VoltageFoundryMod/ForgeSeries/apps/gen/docs/Design.md

# GravityForge — Design

A dual physics-based generative sequencer for the Forge Series hardware.

Two virtual containers hold bouncing balls. Gravity pulls them down, the
containers rotate, and every time a ball strikes a peg on a container wall it
emits a note. The result is a rhythm that is repetitive enough to feel composed
but never quite loops — the Tombola idea, adapted to one encoder and a 128×64
screen.

The novel part of this module is the **proximity coupling**: the two containers
are drawn side by side and a single parameter slides them together. Apart, they
are two independent sequencers. Overlapping, collisions in one shove the balls
in the other. Fully merged, they share one space. It is one continuous knob from
"two sequencers" to "one entangled instrument", and you can see it happening.

---

## 1. Hardware contract

Shared Forge Series platform (XIAO RP2040, SSD1306 128×64, MCP4728 quad DAC,
rotary encoder + switch). See [ForgeSeries-Hardware].

### Inputs

| Jack | Range | Role |
| ---- | --- | --- |
| IN 1 | gate/trigger | Menu-selectable: CLOCK / RESET / KICK / SPAWN |
| IN 2 | **0–5 V** | Assignable modulation target |
| IN 3 | **0–5 V** | Assignable modulation target |

> **CV range.** The current hardware revision accepts **0–5 V only**. A later
> revision moves to ±5 V. Every modulation read therefore goes through a single
> helper, `CvNorm()` in `lib/cvInputs.hpp`, which returns a normalized `0..1`.
> When the bipolar hardware lands, that one function changes to return `-1..1`
> and the targets that want bipolar behaviour opt in via `CvBipolar()` — no
> target-by-target rewrite.

### Outputs

Mirrors NoteForge exactly, so the jack map is muscle memory across the series:

| DAC index | Jack | Signal |
| --- | ---- | --- |
| 0 | 1 | CV A — pitch of the last peg hit, container A |
| 1 | 2 | CV B — pitch of the last peg hit, container B |
| 2 | 3 | GATE A — envelope / trigger / gate |
| 3 | 4 | GATE B |

`OUT_CV(ch)` / `OUT_GATE(ch)` in `lib/pinouts.hpp` name these indices.

---

## 2. Why pegs live on the wall

Tombola draws notes as pegs _inside_ a rotating container. Simulating free-floating
pegs means testing every ball against every peg each step — O(balls × pegs),
which on a 133 MHz Cortex-M0+ with no FPU is the one thing that would blow the
CPU budget.

Putting the pegs **on the container wall** is both closer to the original (the
notes ring the container) and O(1): the wall collision is already being
computed, so the contact angle falls out for free, and the peg index is one
division.

```
contact angle (world)  φ = atan2(py - cy, px - cx)
container-local        φ' = φ - rotation
peg index              i  = floor(φ' / (2π / pegCount))  mod pegCount
```

No search, no per-peg distance test. This is the single decision that makes the
whole module fit in the time budget.

---

## 3. Float, not fixed-point

The first instinct on an FPU-less M0+ is Q16.16 fixed-point. Working the budget
out, that turns out to be unnecessary:

The steady-state (non-colliding) cost per ball per step is ~14 float ops —
integrate velocity and position (8), then the wall test `dx²+dy² > R²` (6). At
the design limit of 8 balls per container × 2 containers × 1 kHz that is
**224 k soft-float ops/sec**, roughly 11 M cycles/sec, or **~8 % of one core**.

The expensive calls — `sqrtf`, `atan2f` — happen only on an actual collision,
which is a handful of events per second per ball, not per step.

So the physics is written in plain `float`, matching the idiom of the rest of
the series (`lib/envelope.hpp`, `lib/quantizer.hpp`) and keeping it readable and
unit-testable. Fixed-point stays available as an optimization if a future
feature (ball–ball collision, many more balls) changes the arithmetic.

**Budget guard:** physics runs at a fixed 1 kHz on Core 0 with a hard cap of
`PHYS_MAX_STEPS_PER_CALL` catch-up steps, so a display stall or a slow I2C write
can never spiral into an unbounded catch-up loop.

---

## 4. Physics model

State per ball: position `(x, y)`, velocity `(vx, vy)`. Semi-implicit Euler at a
fixed 1 ms timestep — fixed-step is what makes the sim deterministic, and
determinism is what makes it unit-testable and identical in VCV Rack.

```
v += g · dt
p += v · dt
```

### Wall collision

A ball is in contact when `|p − c| > R − ballRadius`. On contact:

1. **Project back** onto the wall (prevents tunnelling / sticking).
2. **Reflect** the normal velocity component, scaled by restitution (BOUNCE).
3. **Add the wall's tangential velocity.** The wall is rotating at ω, so the
   contact point is moving at `ω × r`. Transferring a fraction of that
   (the SPIN coupling) is what makes a rotating container actually stir the
   balls rather than just spinning a decorative ring behind them. This is the
   mechanism that makes rotation musical.
4. **Emit** the peg hit for the contact angle, if that peg is enabled.

### Keeping the gate a gate

Three guards decide whether a contact becomes a note, and they are the
difference between a sequencer and a buzzer:

1. **`PEG_MIN_IMPACT_SPEED`** — a peg only speaks when it is actually struck.
   Grazes and settling contacts still resolve as collisions and still transmit
   through the coupling; they just make no note.
2. **Refractory windows** — each ball remembers the last peg it fired.
   Re-striking the same peg needs the full `PEG_REFRACTORY_US`; moving to a
   different one needs the shorter `PEG_MIN_INTERVAL_US`.
3. **`PHYS_MIN_BOUNCE_SPEED`** — a ball that has lost its energy is topped back
   up, so a patch never dies in a silent pile at the bottom. There are two
   different ways that can happen and they need different answers — see
   "Exhausted versus riding" below.

The interaction between (2) and (3) is the subtle part, and getting it wrong is
what turned the GATE jack into a continuous sawtooth in the first version. A
ball settling against a **rotating** wall registers a contact every step, and
because rotation keeps sliding a *new* peg underneath it, the short "different
peg" window applies every time rather than the long one. With the energy floor
set low (6 px/s) the ball vibrated against the rim instead of bouncing, and the
container fired ~33 times a second — the envelope was reset at ~90 % every time
and the output never returned to zero.

The floor therefore has to sit comfortably **above** the impact threshold. At
60 px/s a settled ball hangs for `2×60/220 ≈ 0.55 s`, so it ticks along at about
2 Hz instead of buzzing, and every one of those bounces is hard enough to
count as a strike. The result is ~6 hits/sec per container at the default.

That number then sets container A's envelope default: decay must be shorter than
the gap between notes (~160 ms) or the gate cannot finish, which is why A's
factory decay is 100 ms rather than something pad-like.
`Sequencer.GateReturnsToZeroBetweenHits` is the regression guard.

Container B ships at the opposite end and is sized the other way round — see
"The factory patch is two examples" below.

### GRAVITY as a rescaling of time

Both speed constants above are quoted at `PHYS_REF_GRAVITY` (220) and **scale
with `sqrt(g / PHYS_REF_GRAVITY)`**. While they were absolute, GRAVITY was very
nearly useless as a density control, and for a reason that is invisible from the
formula: the hang-time argument above (`2v/g`) only describes a *vertical* bounce
at the bottom of the bowl. Most contacts are ricochets across a container that is
only `2(R − ballR) = 36 px` wide, and a ball leaving the wall at the 60 px/s floor
crosses a mean chord of `4R/3 ≈ 24 px` in ~0.4 s **whatever gravity is doing**.
Turning gravity down gave flatter paths at the same note rate.

The simulation has exactly one length (`R`) and one acceleration (`g`), so its
natural speed is `sqrt(gR)` — which at the reference works out to 66 px/s, and is
why 60 was the right floor to begin with. Scaling both constants by
`sqrt(g/g₀)` makes GRAVITY a pure rescaling of time: under `v → v/k`,
`g → g/k²` the parabola `x = vt, y = gt²/2` traces the **identical path**, taken
`k` times slower. So the character of the motion, the distribution of contact
angles and the resulting peg pattern are all preserved exactly; only the tempo
moves. Measured, with three balls:

| GRAVITY | scale | hits/sec |
| --- | ----- | --- |
| 5 | 0.15  | 1.0 |
| 30 | 0.37  | 2.1 |
| 220 | 1.00  | 6.1 |
| 900 | 2.02  | 12.3 |

Three consequences worth stating, because each is a bug if forgotten:

- **The scale is floored** at `PHYS_MIN_SPEED_SCALE`. Gravity may legally be 0
  (a container stirred purely by its rotating wall), and an unclamped `sqrt`
  would take the energy floor to zero — balls coasting to a halt — *and* the
  impact threshold to zero, so every graze would speak. That is the buzzer
  failure mode reached from the opposite direction.
- **Reported hit energy is normalised** back into reference units before it
  leaves the physics. ACCENT maps a fixed 30..150 impact window onto gate level
  (`sequencer.hpp`); a slow container reporting its raw, small speeds would make
  every hit read as feather-light and collapse ACCENT to a constant.
- **The coupling uses the receiving container's threshold.** "Was that hard
  enough to ring?" is a question about the rim being struck, and A and B can be
  running very different gravities. Using the source's would let a heavy A
  machine-gun a becalmed B.

`Physics.TheReferenceGravityIsUnscaled` pins the compatibility claim: at 220 the
scale is exactly 1.0 and every number is what it always was.

The **three time constants** — `PEG_REFRACTORY_US`, `PEG_MIN_INTERVAL_US` and
`PHYS_REVIVE_US` — scale _inversely_ with the same factor. Speeds multiply by it,
times divide by it; that is what rescaling time means. Leaving the refractory
windows absolute caps every container at 83 Hz, which is invisible at the
reference where the natural rate is ~6 Hz, and wildly out of scale in a container
whose natural rate is 1 Hz — anything that does chatter down there then runs
completely unchecked.

### Exhausted versus riding

A ball stops making notes in two quite different ways, and conflating them was a
long-standing bug that the gravity scaling made much easier to hit.

**Exhausted** — the ball has genuinely run out of energy and is settling into a
pile at the bottom. Absolute speed is the right measure, an immediate top-up to
`PHYS_MIN_BOUNCE_SPEED` is the right response, and that is the original floor.

**Riding** — the ball has plenty of speed, but SPIN's grip has dragged it up to
the rim's own velocity. `vn`, the quantity that decides whether a strike speaks,
is measured _relative to the wall_, so a co-rotating ball registers nothing while
looking perfectly lively on screen. The absolute floor cannot see this at all: it
looks at a ball travelling at 226 px/s (SPIN 1 at 120 BPM) and correctly declines
to add energy to it.

This was already live before the gravity work: measured at that commit, **SPIN 1
produced 0.02 notes/sec at every gravity** — the container fired once and then
rode the rim in silence indefinitely. It went unnoticed because every physics
test in the suite ran with `omega = 0`. Scaling the speed constants with gravity
then spread the same failure up into the slower spins, since the floor fell below
the rim speed: SPIN 4 was silent at any gravity below ~80, which is exactly where
the ambient settings live.

The fix has two halves, and the second is as important as the first:

1. The floor is also evaluated in the **wall's frame**, which is the frame the
   note-making quantity lives in.
2. That revive is **rate-limited by whether the ball is actually failing to
   speak** — `lastHitUs`, the time of its last real strike. A bare wall-frame
   floor over-corrects badly: a dragged ball is below it on essentially every
   contact, gets re-launched every time, and with the rim sweeping past returns
   within ~10 ms. Measured, that turned the silence into a 45 Hz machine-gun.

So a ball riding the rim gets flicked off it a few times a second rather than
continuously. That is both musical and honest about the physics — a fast-spinning
bowl really does hold its contents against the wall.

One consequence worth stating plainly: **the rotating wall is an energy source
that does not scale with gravity.** At SPIN 1 or 1/2 the wall stirs the container
harder than gravity pulls on it, and GRAVITY loses most of its authority over the
density. SPIN 4 and slower leave it in charge. `Physics.NoSpinAndGravityCombinationGoesSilent`
sweeps all six spin rates × six gravities × both directions, which is the shape
of test this bug needed — any single pair looks fine, and the failure only shows
up as a hole in the grid.

### DENSITY and SPACE

Two controls sit at the very end of the hit path, after the physics has fully
resolved the bounce and after the peg mask:

- **DENSITY** — the percentage chance that a note which cleared everything else
  actually speaks.
- **SPACE** — a minimum gap between two notes from one container, set in beats
  and converted to µs against the live tempo by `ApplyParams()` (the container
  has no clock, exactly as with the loop period).

They exist because *every other* way of thinning the output — fewer balls, less
gravity, less bounce, fewer pegs — also changes how the container moves, and the
screen is half the instrument. A thinned note is a bounce you see and do not
hear, and `Physics.DensityDoesNotDisturbTheMotion` asserts the simulation stays
bit-identical.

SPACE is checked **first**, then DENSITY. SPACE is a hard ceiling on the rate and
DENSITY thins what got through, so the two compose rather than interact: at SPACE
1 beat and DENSITY 50 % you get "at most one note a beat, and about half the
beats speak". The reverse order would have DENSITY rolling dice on notes SPACE
was going to drop anyway.

Only a note that actually *speaks* restarts the SPACE window. Restarting it on a
dropped note would let a busy container gate itself into permanent silence after
its first note — `Physics.SpaceDoesNotStarveAfterDroppingNotes`.

Both live in `Container` rather than in the sequencer so they take part in the
loop snapshot: DENSITY draws from the container's PRNG and SPACE keeps a
timestamp, and if either sat above the snapshot boundary a "repeating" phrase
would quietly gain and lose notes on every pass. See §6.

### The factory patch is two examples

Because the containers are wholly independent at PROXIMITY 0, the boot patch can
be two worked examples rather than one, and it is:

| | A (OUT 1/3) | B (OUT 2/4) |
| --- | --- | --- |
| Rate | ~6.2 notes/s | ~0.45 notes/s |
| Physics | g 220, 3 balls, SPIN 8 | g 20, 1 ball, SPIN 16, bounce 0.45 |
| Notes | C major, SPREAD 2 | C pentatonic major, SPREAD 1, high |
| Gate | 0 / 100 ms | 120 / 750 ms |
| Thinning | none | DENSITY 85, SPACE 2 beats |

A is unchanged from the original factory patch, so patching only OUT 1 still
gives exactly what the module has always given. B exists to make the slow half of
the range audible without the user having to know it is there — which is the
thing a parking-lot feature usually fails at.

Three decisions in B are worth recording:

- **Its scale is a subset of A's.** The containers drift into every possible
  alignment, so B's notes have to be ones that cannot clash with A's whatever
  lands together. C pentatonic major (C D E G A) contains no semitone at all,
  which is what lets it sit under a busy C major sequence indefinitely.
- **SPIN stays slow.** The rotating wall is an energy source that does not scale
  with gravity, so a fast spin here would stir the container harder than gravity
  pulls on it and undo the slowness GRAVITY was set for.
- **The envelope is sized against SPACE's floor, not the average gap.** B averages
  ~2.3 s between notes but SPACE only guarantees 1 s, so attack + decay is
  120 + 750 = 870 ms. Sizing it against the average would look right on paper and
  clip on every close pair — the same mistake as A's decay, one order of
  magnitude further out.

`Physics.FactoryContainersSitAtOppositeEndsOfTheRange` pins the behaviour; the
Rack isolation test pins the settings themselves, including that the envelope
fits inside the SPACE floor.

---

## 5. Proximity coupling

Both containers have radius `R` and sit on the screen midline. A single
**PROXIMITY** parameter (0–100 %) sets the distance `D` between their centres:

```
D = D_MAX − proximity/100 × (D_MAX − D_MIN)

PROXIMITY 0%              PROXIMITY 55%           PROXIMITY 100%
   ___     ___              ___ _ ___                 _____
  / A \   / B \            / A X B \                 / AB  \
 |     | |     |          |    |    |               |       |
  \___/   \___/            \___|___/                 \_____/
    independent            overlap: coupled          merged: one space
```

Overlap fraction `k = clamp((2R − D) / 2R, 0, 1)` is the coupling strength.

When `k > 0` and a ball in A strikes the wall **at a contact point that lies
inside container B**, the collision transmits: an impulse is applied to B's
balls, directed away from the contact point, scaled by `k` and by the collision
energy, and falling off with distance. Symmetrically for B → A.

This is deliberately _energy_ transfer, not ball transfer. It means:

- the ball count in each container is stable and predictable
- each container keeps its own scale, peg layout and gravity

### What a transmitted strike plays

The energy arrives at a point on the receiving rim, so **the peg there rings** —
a real note and gate on that channel. The note is entirely the receiving
container's own (its peg ring, its scale, its SPREAD/BIAS, its muted pegs), so
nothing is copied across and a transfer can never sound out of key. Muting a peg
absorbs the transfer silently, which is how you shape which transfers speak.

Transmitted energy is scaled by COUPLE **before** the impact test, which is what
turns COUPLE into a musical gradient rather than an on/off switch — light
coupling only nudges trajectories, and the containers begin answering each other
audibly only as it comes up:

| PROXIMITY | COUPLE | A notes/s | B notes/s | transmitted/s | |
| --- | --- | --- | --- | --- | --- |
| 0 % | 60 % | 6.1 | 4.1 | 0.0 | apart — baseline |
| 60 % | 0 % | 6.4 | 4.6 | 0.0 | overlapping, coupling off |
| 60 % | 30 % | 6.0 | 4.2 | 3.8 | transmitting, too weak to ring |
| 60 % | 100 %  | 7.6 | 6.1 | 3.5 | starting to answer |
| 100 % | 100 %  | 10.3 | 9.9 | 10.5 | fully entangled |

Density roughly doubles at the extreme, which is the point of that setting. The
GATE jack still articulates there — measured 10.3 Hz, 0.00–5.00 V, idle 39 % of
the time with the 100 ms factory decay.

Transmitted strikes carry their own refractory, separate from the per-ball one,
because there is no ball behind them.

### Making it legible

The impulse is strong — measured against an identical uncoupled world it
displaces balls by **~13 px on a 40 px container**:

| PROXIMITY | separation | overlap | transmitted strikes/s | displacement |
| --- | --- | --- | --- | --- |
| 0 % | 48 | 0.00 | 0.0 | 0.00 px |
| 40 % | 28.8 | 0.28 | 3.0 | 13.5 px |
| 100 % | 0 | 1.00 | 12.4 | 13.6 px |

But strength was never the problem. Coupling fires a handful of times a second
while both containers are *already* bouncing several times a second, so with
nothing tying cause to effect the control reads as if it does nothing at all —
you cannot see a counterfactual.

So a transmitted strike raises a **spark**: an expanding double ring drawn at the
contact point for a few frames. That one cue is what turns PROXIMITY from
"apparently inert" into something you can watch working.
`Physics.CouplingRaisesAVisibleSpark` guards it.

Note the tests here deliberately assert *magnitude*, not mere non-zero
divergence. An earlier version only checked the two worlds differed by 0.01 px,
which any chaotic perturbation satisfies — it would have passed even if coupling
were imperceptible.

### Portals — deferred

Ball _transfer_ between containers is a natural extension of exactly this
geometry: the arc of A's wall that lies inside B is already computed, so opening
it and moving the ball into B is a small change. It is deliberately **not** in
v1 — it makes ball counts drift, and it is easy to end up with every ball in one
container and silence in the other. `PhysicsWorld::OverlapArc()` is written and
tested so this stays cheap to add later.

---

## 6. Timing

Physics **always free-runs.** Collisions produce note events the instant they
happen — that organic, never-quite-on-grid feel is the whole point.

Optionally, those events can be deferred to a clock grid:

```
QUANTIZE:  OFF | 1/4 | 1/8 | 1/16 | 1/8T | 1/16T
```

With quantize on, a peg hit is queued and released on the next division
boundary. **Drop rule:** if a second hit arrives for the same channel before the
pending one is released, the newer hit replaces it (last-wins). Stacking would
produce a burst of retriggers at the boundary; last-wins keeps the density
sounding like the physics that produced it.

The clock itself is the internal BPM (20–300, default 120), or an external clock
at IN 1 when that jack's role is CLOCK (interval between edges → BPM, median of
the last few intervals so one jittery edge does not lurch the tempo).

### Configured vs actually running

`Clock` tracks two separate things, and conflating them is a bug:

- `IsExternal()` — IN 1 is *configured* as a clock input. A menu setting.
- `IsExternalLive()` — and pulses are *actually arriving* right now.

The hardware has no switched jacks, so it cannot tell a patched cable from an
unpatched one — but it can tell whether edges are coming in, and that is the
thing that matters. CLOCK is IN 1's default role, so keying anything off
`IsExternal()` means the module declares itself externally clocked from the
moment it powers on, and the "e" badge on the home screen never tells you
anything.

Liveness needs a measured *interval*, not just one edge, and it lapses if no
pulse arrives within three intervals (clamped to 0.5–5 s). Scaling the timeout
to the observed tempo matters: a 30 BPM clock at 1 ppqn is 2 s between pulses,
so a short fixed timeout would declare it dead between every beat, while a long
fixed one would leave a fast clock hanging for seconds after it stops.

When liveness lapses the tempo falls back to the internal BPM and the interval
history is cleared. Without that, unplugging a clock leaves the containers
turning at whatever tempo was last derived, with the internal setting ignored
for ever.

Rotation is tied to the clock rather than set in raw degrees/sec, so the
containers stay musically related to the patch: **SPIN** selects beats per
revolution (`1/2/4/8/16`, plus reverse), and there is a FREE setting for when you
want it detached.

### Loop mode — keeping a phrase

The module's one real weakness is that a passage you like is gone before you can
reach the encoder. The fix falls out of determinism: the same state, stepped the
same number of times, produces the same notes. So a phrase is nothing more than a
snapshot plus a step count. Capture the balls, the rotation and the `PhysRandom`
state; run N beats' worth of steps; put it all back.

Three decisions make it hold together, and each of them is the difference
between a phrase that repeats and one that only nearly repeats:

**The rewind lands on an exact step, not on elapsed time.** `LoopTick()` runs
inside `PhysicsWorld::Advance()`'s stepping loop and counts steps. Scheduling it
from wall time would put the boundary a step early or late depending on how the
caller was interrupted, and one step of divergence in a chaotic system is a
different phrase within a few repeats.

**The simulation runs on its own clock.** `_simUs` advances exactly
`PHYS_STEP_US` per step and is what the peg refractory windows are measured
against. Previously the wall time was passed down, which meant identical ball
states could clear a 12 ms window on one pass and miss it on the next depending
on how many catch-up steps a call happened to batch. Free-running that is
invisible; looping it is fatal.

**Hit timestamps travel as ages, not absolute times.** The refractory guards ask
"how long since this ball last spoke". A restored absolute timestamp would sit
further into the past on every repeat, so the first bounce of each loop would
eventually clear a window it had not cleared the first time and the phrase would
gain a note it never contained.

What is deliberately _not_ snapshotted is the parameter set — gravity, spin, the
peg mask, proximity, the scale. Restoring those would make the loop fight the
menu and freeze CV modulation, when the reason to lock the motion is so you can
keep playing everything else over the top of it.

**NAP/WAKE** then mutes whole loops per container, with **SHIFT** offsetting each
container's place in that cycle — wake 1 / nap 1 with B shifted by one is
call-and-response for the cost of one menu row. The physics keeps running through
a nap and only the voice is silenced (`GravityChannel::SetMuted`), so a container
returns exactly where it would have been rather than restarting.

A change to **BEATS** re-arms and captures a new phrase; a change of _tempo_ does
not, or an external clock wandering by a BPM would re-arm every pass and the loop
would never repeat at all. `Reset()` re-arms too, which is what gives Randomize a
freshly captured phrase without any code of its own.

---

## 7. Pitch

Reuses NoteForge's `Quantizer` and `scales.hpp` unchanged — the peg ring is
just an index into the quantizer's table of enabled semitones.

Everything is counted in **scale degrees**, never semitones, so no combination of
settings can produce an out-of-key note, and the interval between adjacent pegs
follows the scale — a third in major, something else in pentatonic. Same
reasoning as NoteForge's degree-based transposition.

### SPREAD and BIAS

There is deliberately **no separate octave row.** An octave offset on its own only
slides the ring up and down; it says nothing about how wide the ring is or how the
notes sit inside it. So the register lives on the ROOT row it belongs to (see
"Where the span sits" below) and the two rows it would have cost do the work an
offset cannot:

- **SPREAD** — how many octaves the ring covers (1–5), counted up from ROOT and
  independent of peg count.
- **BIAS** — where inside that span the notes crowd (−100 low … 0 even … +100 high).

```
peg i   t     = i / (pegCount - 1)              fraction around the ring
        gamma = 2^(-|bias| / 70)                always <= 1
        warp  = bias >= 0 ?  t^gamma            crowd high
                          :  1 - (1-t)^gamma    crowd low  (mirror image)
        degree   = base + round(warp * span)
        semitone = quantizer.SemitoneAt(degree)
```

Warping `t` moves the notes in between **without moving the ends** (measured,
and asserted by `Sequencer.BiasTableMatchesTheDocumentedNotes`):

```
8 pegs, C major, ROOT C4, SPREAD 2   (0–2 V)

BIAS   0  (even)    C4  E4  G4  B4  D5  F5  A5  C6
BIAS -100 (low)     C4  D4  E4  F4  G4  A4  C5  C6
BIAS +100 (high)    C4  C5  E5  F5  G5  A5  B5  C6
```

Fixed endpoints are what make the two controls independent: the ring always
covers exactly the octaves SPREAD asks for, and BIAS only decides the
distribution inside it.

The two directions are **mirror images** rather than `gamma` vs `1/gamma`,
because the warp is discretised onto whole scale degrees. A steep curve near
`t = 0` rounds several pegs onto the same bottom note while the same curve near
`t = 1` spreads them out, so a plain `t^gamma` crowded low far harder than it
crowded high — at full negative bias it stacked three of eight pegs onto the
root while full positive bias produced no duplicates at all. Mirroring makes the
control behave identically in both directions, and neither extreme stacks pegs.

### Where the span sits — ROOT is an absolute note

**The ring starts on ROOT and opens upward by SPREAD.** ROOT therefore carries an
octave — it is `C4`, not `C` — and it is the module's register control.

It did not always work that way, and the first version is instructive. With ROOT
as a bare pitch class nothing anchored the register, so the span was **centred in
the output range and snapped to whole octaves**: a reasonable-sounding rule that
turns out to be unusable, because the one thing the user cannot then do is
choose where the notes are. Two pegs over one octave landed two octaves up, and
no control on the module would move them. "Centred" is a decision the module has
no business making — it is the first thing a player wants to state.

Folding the octave into ROOT rather than adding a row is forced by the six-row
page limit, and it turns out to be the better UI anyway: "the ring starts on this
note" is one idea, and the row that names the note is where you look for it. The
menu edits it as a single semitone number so one detent is a semitone, and the
displayed octave has 0V NOTE applied, so the row reads as the note the
oscillator will play.

The octave is capped at `QUANT_OCTAVES - SPREAD` so the whole ring fits under
5 V, and widening SPREAD walks ROOT down rather than letting the top of the ring
flatten against the ceiling. A root part-way up the top octave can still leave
the ring a degree or two short of its full span; `SemitoneForPeg` covers less
rather than stacking the last pegs onto one note, which reads as a fault.

The lowest peg is the root itself — `IndexAtOrAbove`, never the _nearest_ degree,
so a hand-edited note mask that switches the root off moves the ring up to the
next available note instead of below the note the row names.

### What the notes are called — 0V NOTE

The jacks are the MCP4728's **0–5 V and nothing else**: five octaves at 1 V/oct,
with no negative rail to reach below 0 V. So the one thing the module can get
wrong about pitch is not the voltage but the _name_ — which note the patch
considers 0 V to be. That is a fact about the oscillator on the other end of the
cable, not about this module, so it is a setting: **SETTINGS ▸ 0V NOTE**, C0–C5,
default **C4** (VCV Rack's convention, and the common one on hardware VCOs).

Everything follows from it:

```text
volts(note) == octave(note) - 0V NOTE

0V NOTE = C4    range C4 (0 V) .. C9 (5 V),   SPREAD 2 ring = C6..C8
0V NOTE = C2    range C2 (0 V) .. C7 (5 V),   SPREAD 2 ring = C4..C6
```

It renames, it never transposes — the voltage on the jack is identical at every
setting, and SPREAD keeps sole control of where inside the range the notes sit.
Naming it after the thing it sets ("the note at 0 V") rather than REF or TUNING
is deliberate: both of those read as if turning them moves the pitch, which on
unipolar hardware is the one thing it cannot do.

It was previously fixed at C0, which is why a note the screen called C2 came out
of a Rack VCO — where 0 V is C4 — as C6. The setting is stored in the preset, so
a patch keeps the tuning of the rack it was built in.

Because a peg's pitch now depends on the peg *count* (it sets where each peg
falls within the span), the count travels with the hit — including a deferred
one, whose count must be the one that was in force when the ball actually
struck.

Per container: scale, root (with its octave), spread, bias, peg count (4–16), and
a peg enable mask so individual pegs can be silenced to open up the rhythm.

---

## 8. Screen

`R = 20 px`, centres on `y = 32`, so the containers occupy rows 12–52 and leave
a header row and a footer row.

```
 0        BPM 120   SPIN 4   CPL 55%          <- header
 12   .-""-.   .-""-.
      /  o   \ /   *  \                        <- containers slide together
 32  |    o   X   *    |                          with PROXIMITY
      \   .  / \  o   /
 52    '-..-'   '-..-'
 54       C3            G4                     <- live note per channel
```

Pegs are drawn on the wall: a solid 5 px dot when enabled, a small hollow ring
when muted, and a 7 px blob for a few frames after firing. Sizes are set by the
tightest case — at 16 pegs the rim gives 7.9 px of spacing, so a 5 px dot still
leaves clear air between neighbours while the 7 px flash fills the gap and makes
a hit unmistakable.

Balls are drawn at their true simulated radius (`PHYS_BALL_R`, 5 px across) —
filled for container A, hollow-with-a-centre-dot for B, so the two populations
stay distinguishable once PROXIMITY merges them into one space. Drawing the real
radius is the point of working in screen pixels: the ball you see is the ball
being simulated, so it never appears to sink into or float off the wall.

Rendering runs on **Core 1** exactly as in NoteForge, so the 20 Hz redraw never
stalls the 1 kHz physics on Core 0.

---

## 9. Menu map

| Group | Page | Contents |
| ----- | --- | --- |
| 0 | HOME | the physics view (custom renderer) |
| 1 | CLOCK | BPM, spin, quantize, IN1 role |
| 2 | COUPLING  | proximity, coupling amount, reset/kick actions |
| 3 | A PHYSICS | gravity, bounce, balls, spin ratio |
| 4 | B PHYSICS | same, container B |
| 5 | LOOP | phrase length, nap/wake, shift, new phrase |
| 6 | A NOTES | scale, root+octave, spread, bias, pegs, density |
| 7 | B NOTES | same, container B |
| 8 | A GATE | mode, attack, decay, level |
| 9 | B GATE | same, container B |
| 10 | CV | IN2 target, IN3 target, depths |
| 11 | SETTINGS  | 0V NOTE, screen timeout, boot menu |

LOOP sits after the two PHYSICS pages rather than next to CLOCK: its shift and
nap/wake settings are read per container, so it belongs with the rest of the
per-container editing rather than in the clock-domain block at the top.

Every page except HOME is a plain list handled by the existing generic
`MD_RenderGroup()` — no new rendering code per page.

---

## 10. File map

New to this module:

| File | Purpose |
| --- | --- |
| `lib/physics.hpp` | `Ball`, `Container`, `PhysicsWorld` — the simulation and coupling |
| `lib/sequencer.hpp`  | `GravityChannel` — container + peg→note mapping + envelope |
| `lib/clock.hpp` | internal/external clock, spin rate, quantize grid |
| `lib/cvInputs.hpp` | 0–5 V acquisition, `CvNorm()`, target matrix, IN 1 role |
| `lib/menuRender.hpp` | the physics home screen |

Carried over from NoteForge essentially unchanged: `quantizer.hpp`, `scales.hpp`,
`envelope.hpp`, `displayManager.hpp`, `menuDisplay.hpp`, `menuDefinitions.hpp`,
`boardIO.hpp`, `storage.hpp`, `calibration.hpp`, `calibrationData.hpp`,
`encoder.hpp`, `utils.hpp`, `splash.hpp`.

---

## 11. Constraints inherited from the platform

- Anything in `lib/` must compile for **both** the RP2040 and the VCV Rack shim.
- Core 1 owns `Wire` (display); Core 0 owns `Wire1` (DAC). Never cross them.
- `micros()` is the only clock — every time-dependent subsystem takes the
  timestamp as a parameter, which is what makes it testable and makes the VCV
  port deterministic under faster-than-realtime rendering.
- New mutable file-scope globals must be registered in the VCV port's
  `engine_state.def`, or Rack instances will share them.
- Changing `LoadSaveParams` invalidates saved slots — bump `VALID_MAGIC`.
