VoltageFoundryMod/ForgeSeries/apps/clk/docs/XIAO_RP2040.png

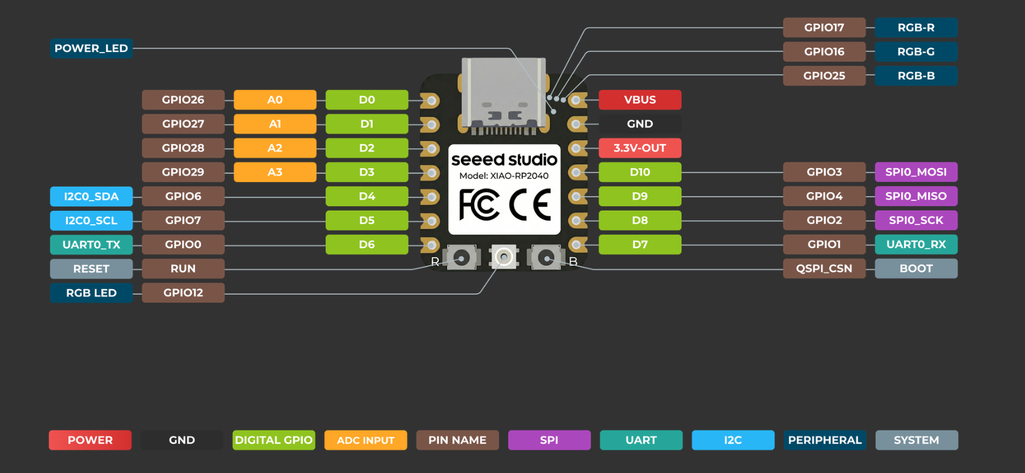
apps/clk/docs/XIAO_RP2040.png
