VoltageFoundryMod/ForgeSeries/core/menuDisplay.hpp

#pragma once
// ============================================================
// menuDisplay.hpp — Composable display primitives for the menu
// system.  All functions operate on the global `display` object
// and the global `menuItem` / `menuMode` state from main.cpp.
//
// Included once from main.cpp (after menuDefinitions.hpp and
// menuHandlers.hpp).
// ============================================================

// App-supplied hooks. These are deliberately the ONLY externs here: when an app
// TU is wrapped in namespace forge::<app>, this header is included from inside
// that namespace so these resolve to that app's own implementations.
//
// The board-owned objects this header also uses — `display` above all — are
// declared in core/shellObjects.hpp instead, which is included at global scope.
// Declaring `display` here would have namespaced it too, giving every app a
// private framebuffer. See that header for the full explanation.
extern void RedrawDisplay();
extern void MenuHeader(const char *header);

// ── Layout constants ─────────────────────────────────────────
// The header occupies rows 1–8, so the first row starts at 12. With 9px rows
// that puts a six-row page at y = 12,21,30,39,48,57 — the last row's glyphs end
// on row 63, exactly filling the 64px screen. Do not raise MD_START_Y without
// checking the longest page (SCALES and PITCH both have six rows): at 20 the
// sixth row lands at y=65 and is silently clipped.
static const int MD_ROW_H = 9;    // pixels per row
// Overridable: ClockForge's generic group pages sit at 20. A macro rather than
// a const so an app can set it before including this header.
#ifndef MD_START_Y
#define MD_START_Y 12 // first row Y (below header)
#endif
static const int MD_LABEL_X = 10; // left edge for row labels
static const int MD_VALUE_X = 70; // default single-column value X
static const int MD_CURSOR_X = 1; // cursor triangle left edge

// Cursor triangle: hollow = selected, filled = editing
static inline void _MD_Cursor(int y, bool sel, bool editing) {
    if (!sel)
        return;
    if (editing)
        display.fillTriangle(MD_CURSOR_X, y - 1, MD_CURSOR_X, y + 7, MD_CURSOR_X + 4, y + 3, 1);
    else
        display.drawTriangle(MD_CURSOR_X, y - 1, MD_CURSOR_X, y + 7, MD_CURSOR_X + 4, y + 3, 1);
}

// Draw header + reset internal row counter.  Returns starting Y.
static int _md_rowY;
static inline void MD_PageBegin(const char *title, int startY = MD_START_Y) {
    display.setTextSize(1);
    MenuHeader(title);
    _md_rowY = startY;
}

// Single-column row: label at MD_LABEL_X, value at MD_VALUE_X.
static inline void MD_Row(const char *lbl, String val, bool hasVal,
                          bool sel, bool editing) {
    display.setCursor(MD_LABEL_X, _md_rowY);
    display.print(lbl);
    if (hasVal) {
        display.setCursor(MD_VALUE_X, _md_rowY);
        display.print(val);
    }
    _MD_Cursor(_md_rowY, sel, editing);
    _md_rowY += MD_ROW_H;
}

// Single-column row with a custom value X.
static inline void MD_RowAtX(const char *lbl, String val, bool hasVal, int valX,
                             bool sel, bool editing) {
    display.setCursor(MD_LABEL_X, _md_rowY);
    display.print(lbl);
    if (hasVal) {
        display.setCursor(valX, _md_rowY);
        display.print(val);
    }
    _MD_Cursor(_md_rowY, sel, editing);
    _md_rowY += MD_ROW_H;
}

// Action row: label only, no value.
static inline void MD_ActionRow(const char *lbl, bool sel) {
    display.setCursor(MD_LABEL_X, _md_rowY);
    display.print(lbl);
    if (sel)
        display.drawTriangle(MD_CURSOR_X, _md_rowY - 1, MD_CURSOR_X, _md_rowY + 7, MD_CURSOR_X + 4, _md_rowY + 3, 1);
    _md_rowY += MD_ROW_H;
}

// Two-column row: label, val1 at x1, val2 at x2.
static inline void MD_TwoColRow(const char *lbl, String v1, bool hasV1,
                                String v2, bool hasV2,
                                int x1, int x2, bool sel, bool editing) {
    display.setCursor(MD_LABEL_X, _md_rowY);
    display.print(lbl);
    if (hasV1) {
        display.setCursor(x1, _md_rowY);
        display.print(v1);
    }
    if (hasV2) {
        display.setCursor(x2, _md_rowY);
        display.print(v2);
    }
    _MD_Cursor(_md_rowY, sel, editing);
    _md_rowY += MD_ROW_H;
}

// Blank gap (just advances _md_rowY without printing anything).
static inline void MD_Gap(int px = MD_ROW_H) {
    _md_rowY += px;
}

// Finish a page — calls RedrawDisplay().
static inline void MD_PageEnd() {
    RedrawDisplay();
}

// ── Two-column page renderer ──────────────────────────────────
// A page whose items are ROW_TWOCOL/ROW_HIDDEN pairs, under a row of column
// headers with an indicator arrow marking which column the encoder is editing.
// ClockForge has several of these (level/offset, state/invert, swing, cross
// ops, phase/duty) and they were five copies of the same 28 lines.
//
// Each column is described by its header text, the x the header prints at, and
// the x its indicator arrow sits at. The arrow x is passed rather than derived
// because the existing pages do not agree on the gap (some use 5px, some 6px)
// and this renderer has to reproduce them exactly.
struct MD_ColSpec {
    const char *hdr; // column header text
    int hdrX;        // x the header prints at
    int arrowX;      // x the active-column indicator sits at
};

// WHICH COLUMN IS ACTIVE is read off the item's own rowStyle, never off the
// parity of its item number.
//
// Every one of these pages used to test `menuItem % 2`, which worked only
// because of where the rows happened to land in MENU_ITEMS[] — and already had
// to be inverted for cross ops, whose rows start on an odd number. Any
// reordering of the menu silently pointed the arrow at the wrong column, with
// nothing to catch it. The pairing itself is what the test should read: the
// ROW_TWOCOL item owns the left column and its ROW_HIDDEN partner the right.
//
// `allowEdit` is false for pages built from MENU_TOGGLE items, which never
// enter edit mode and so always draw a hollow cursor.
// startY is where the COLUMN HEADER goes, one row above the page grid, so the
// data rows beneath it land on exactly the same y values a single-column page
// uses. Scrolling between the two kinds of page then moves the cursor down a
// row rather than nudging every label a pixel or two sideways of where the eye
// left it — these pages sat at three different offsets before.
//
// Derived rather than written down, so it follows MD_START_Y if that moves.
static bool MD_RenderTwoColPage(const char *title,
                                int curItem, // 1-based menuItem
                                int curMode, // menuMode
                                int groupId,
                                MD_ColSpec c1, MD_ColSpec c2,
                                bool allowEdit,
                                int startY = MD_START_Y - MD_ROW_H) {
    MD_PageBegin(title, startY);

    display.setCursor(c1.hdrX, _md_rowY);
    display.println(c1.hdr);
    display.setCursor(c2.hdrX, _md_rowY);
    display.println(c2.hdr);

    const bool leftActive =
        (curItem >= 1 && curItem <= MENU_ITEM_COUNT)
            ? (MENU_ITEMS[curItem - 1].rowStyle != ROW_HIDDEN)
            : true;
    const int ax = leftActive ? c1.arrowX : c2.arrowX;
    display.fillTriangle(ax, _md_rowY, ax, _md_rowY + 6, ax + 3, _md_rowY + 3, 1);
    _md_rowY += MD_ROW_H;

    // One visible row per pair: the ROW_TWOCOL item draws both values, and the
    // cursor shows on it when either half of the pair is selected.
    for (int i = 0; i < MENU_ITEM_COUNT; i++) {
        const MenuItem &mi = MENU_ITEMS[i];
        if (mi.group != groupId || mi.rowStyle == ROW_HIDDEN)
            continue;
        const int idx = i + 1;     // the ROW_TWOCOL item
        const int idxPair = idx + 1; // its ROW_HIDDEN partner
        const bool sel = (idx == curItem || idxPair == curItem);
        const bool edit = allowEdit && sel && (curMode == curItem);
        MD_TwoColRow(mi.label,
                     mi.valueFn ? mi.valueFn() : String(""), mi.valueFn != nullptr,
                     mi.valueFn2 ? mi.valueFn2() : String(""), mi.valueFn2 != nullptr,
                     mi.col1x, mi.col2x, sel, edit);
    }
    return true;
}

// ── Generic group renderer ────────────────────────────────────
// Renders all items that share a group id using their rowStyle /
// valueFn / valueFn2 / label fields.  Every non-home page in this
// firmware is a plain list, so this handles all of them.
static bool MD_RenderGroup(const char *title,
                           int curItem, // 1-based menuItem
                           int curMode, // menuMode
                           int groupId,
                           int startY = MD_START_Y) {
    MD_PageBegin(title, startY);
    for (int i = 0; i < MENU_ITEM_COUNT; i++) {
        const MenuItem &mi = MENU_ITEMS[i];
        if (mi.group != groupId)
            continue;
        int idx = i + 1; // 1-based item number
        bool sel = (idx == curItem);
        bool edit = sel && (curMode == idx);

        switch (mi.rowStyle) {
        case ROW_ACTION:
            MD_ActionRow(mi.label, sel);
            break;
        case ROW_TWOCOL:
            MD_TwoColRow(mi.label,
                         mi.valueFn ? mi.valueFn() : String(""), mi.valueFn != nullptr,
                         mi.valueFn2 ? mi.valueFn2() : String(""), mi.valueFn2 != nullptr,
                         mi.col1x, mi.col2x, sel, edit);
            break;
        case ROW_HIDDEN:
            break;
        case ROW_SINGLE:
        default:
            MD_RowAtX(mi.label,
                      mi.valueFn ? mi.valueFn() : String(""), mi.valueFn != nullptr,
                      mi.col1x, sel, edit);
            break;
        }
    }
    return true;
}
