VoltageFoundryMod/ForgeSeries/apps/clk/vcv-plugin/src/plugin.cpp

#include "plugin.hpp"


Plugin* pluginInstance;


void init(Plugin* p) {
	pluginInstance = p;

	// Add modules here
	p->addModel(modelClockForge);
	p->addModel(modelClockForgeExpander);

	// Any other plugin initialization may go here.
	// As an alternative, consider lazy-loading assets and lookup tables when your module is created to reduce startup times of Rack.
}
