VoltageFoundryMod/ForgeSeries/apps/clk/vcv-plugin/src/plugin.hpp

#pragma once
#include <rack.hpp>


using namespace rack;

// Declare the Plugin, defined in plugin.cpp
extern Plugin* pluginInstance;

// Declare each Model, defined in each module source file
extern Model* modelClockForge;
extern Model* modelClockForgeExpander;
