VoltageFoundryMod/ForgeSeries/core/calibration.hpp

#pragma once

// calibration.hpp — Hardware calibration wizard
//
// Entry point: RunCalibration()
// Called by the shell from the CALIBRATE row of the module selector, which is
// the one place it belongs: calibration describes the board's analog front and
// back ends, not any one module, and the same /cal.bin then serves every app.
//
// It runs on Core 0 with Core 1 still parked (see src/main.cpp), so it
// owns the display outright and calls display.display() itself — there is no
// frame-ready handshake to observe here, and no app is running to fight over it.
//
// Worth running even though every module ships usable without it, and most of
// all before running NoteForge: a quantizer's whole job is turning input volts
// into the *right* semitone, and an uncalibrated ADC gain error walks the output
// off by a semitone or more towards 5V.
//
// Step 1 — Output trim (full-scale anchor):
//   All 4 outputs driven to MAXDAC (5V after hardware trimming).
//   User adjusts the on-board trimmers with a multimeter until each jack
//   reads 5.00V.  Press encoder to proceed.
//
// Step 2 — Output low-point offset capture:
//   All 4 outputs driven to the ideal-1V code (calibration bypassed).  For each
//   channel the user measures the jack and dials the reading in with the encoder.
//   With the full-scale anchor from Step 1 this gives a per-channel command
//   remap (dacScale/dacOffset) that removes the residual op-amp offset.  The
//   module cannot read its own outputs, hence the manual entry.
//
// Steps 3–6 — CV input 2-point linear capture:
//   For each channel (CV1, CV2) at each reference voltage (1V, 3V):
//     User applies an external reference to the CV input jack.
//     Display shows the live ADC reading as an estimated voltage so the user
//     can confirm the signal is stable before clicking.
//     On click: 256 samples are averaged and stored.
//   Two readings per channel (1V + 3V) define a linear mapping:
//       mv = cvScale * raw_adc + cvOffset
//
// CalibrationData is persisted by the shell's SaveCalibration(), which writes
// the shared /cal.bin on the filesystem. It survives a firmware flash.

#include <Adafruit_SSD1306.h>
#include <Arduino.h>

#include "boardIO.hpp"
#include "encoder.hpp"

// Forward declaration from the shell (src/main.cpp).
extern void SaveCalibration(const CalibrationData &);

// ── Calibration constants ────────────────────────────────────────────────────
static const int CAL_ADC_SAMPLES = 256; // samples averaged per capture point per channel

// Output low-point capture: drive the DAC to the code that ideally yields 1.000V
// and have the user measure the true jack voltage. Paired with the trimmed
// full-scale anchor (MAXDAC → 5.000V) this fixes the op-amp offset.
static const int CAL_DAC_LOW_MV = 1000;                             // ideal low point (mV)
static const int CAL_DAC_LOW_CODE = MAXDAC * CAL_DAC_LOW_MV / 5000; // = 819 counts

// Jack names for the prompts. Physical, not module-flavoured: the wizard runs
// from the module selector, before an app has been chosen, so "OUT 3" is the
// only name that is true whichever one you go on to boot.
static const char *const CAL_OUT_NAMES[NUM_MAX_OUTPUTS] = {
    "OUT 1", "OUT 2", "OUT 3", "OUT 4", "OUT 5", "OUT 6", "OUT 7", "OUT 8"};

// How much hardware this run is calibrating. Decided by probing the DAC bus,
// NOT by any module's EXPANDER setting: the wizard runs from the shell's
// module selector, before an app has been chosen, so there is no app setting
// to read — and the physical question ("is a second DAC answering?") is the
// right one anyway.
// inline, not static: core/'s rule, because a file-scope static gives every
// including TU its own copy of what is one piece of state. Only src/main.cpp
// includes this header today, so static would work — the const tables above
// stay static for that reason — but these three are mutable, and that is
// exactly what the rule exists to catch.
inline int _calOuts = NUM_OUTPUTS;
inline int _calCvIns = NUM_CV_INS;
// Steps: output trim, output offsets, then two references per CV input.
inline int _calSteps = 2 + 2 * NUM_CV_INS;

// ── Helpers ──────────────────────────────────────────────────────────────────

static void _CalClear() {
    display.clearDisplay();
    display.setTextColor(WHITE);
    display.setTextWrap(false);
}

static void _CalHeader(const char *title) {
    _CalClear();
    display.setTextSize(1);
    display.setCursor(0, 0);
    display.print(title);
    display.drawLine(0, 9, 127, 9, WHITE);
}

// Push the prepared frame to the panel. Core 1 is parked while the wizard runs,
// so this core owns Wire and writes it directly (~28ms for 128×64 @ 400kHz).
static void _CalFlush() { display.display(); }

// Block until the encoder button is pressed then released (with debounce).
static void _CalWaitClick() {
    while (digitalRead(ENCODER_SW) == LOW)
        delay(10); // wait for release if still held
    delay(20);
    while (digitalRead(ENCODER_SW) == HIGH)
        delay(10); // wait for press
    delay(20);
    while (digitalRead(ENCODER_SW) == LOW)
        delay(10); // wait for release
    delay(20);
}

// Average CAL_ADC_SAMPLES raw ADC readings from one pin.
// 200µs between samples to let the ADC input settle between reads.
static uint16_t _CalReadADC(int pin) {
    uint32_t sum = 0;
    for (int i = 0; i < CAL_ADC_SAMPLES; i++) {
        sum += analogRead(pin);
        delayMicroseconds(200);
    }
    return (uint16_t)(sum / CAL_ADC_SAMPLES);
}

// Return a single raw ADC reading from a pin (used for live display).
static uint16_t _CalReadADCRaw(int pin) { return (uint16_t)analogRead(pin); }

// ── Encoder-driven voltage entry ─────────────────────────────────────────────
// Let the user dial a voltage (mV) with the encoder (1 mV per detent) and
// confirm with a click.  Used for output-offset capture, where the module
// cannot read its own output and must be told the multimeter reading.
static int _CalEnterMV(const char *title, const char *prompt, int startMV) {
    int valMV = constrain(startMV, 0, 5000);
    long base = encoder.read();
    bool redraw = true;

    // We were called just after a click — wait for release before accepting input.
    while (digitalRead(ENCODER_SW) == LOW)
        delay(10);
    delay(20);

    while (true) {
        // Poll the encoder often so detents are not missed (shim: ±4 counts/detent).
        long detents = (encoder.read() - base) / 4;
        if (detents != 0) {
            valMV = constrain(valMV + (int)detents, 0, 5000);
            base += detents * 4;
            redraw = true;
        }
        if (redraw) {
            _CalHeader(title);
            display.setTextSize(1);
            display.setCursor(0, 13);
            display.println(prompt);
            display.setTextSize(2);
            display.setCursor(0, 28);
            display.printf("%d.%03dV", valMV / 1000, valMV % 1000);
            display.setTextSize(1);
            display.setCursor(0, 56);
            display.print("Turn=set Click=save");
            _CalFlush();
            redraw = false;
        }
        // Confirm on click (debounced), then wait for release.
        if (digitalRead(ENCODER_SW) == LOW) {
            delay(20);
            if (digitalRead(ENCODER_SW) == LOW) {
                while (digitalRead(ENCODER_SW) == LOW)
                    delay(10);
                delay(20);
                return valMV;
            }
        }
        delay(3);
    }
}

// Convert a raw 12-bit ADC value to an approximate display voltage in mV.
static uint32_t _CalRawToMVDisplay(uint16_t raw) {
    return (uint32_t)raw * 5000 / MAXADC;
}

// ── Phase 1: Output trim ──────────────────────────────────────────────────────
static void _CalOutputTrim() {
    DACWriteAll(MAXDAC, MAXDAC, MAXDAC, MAXDAC);
    if (_calOuts > NUM_OUTPUTS)
        DACWriteAllExp(MAXDAC, MAXDAC, MAXDAC, MAXDAC);

    char title[24];
    snprintf(title, sizeof(title), "1/%d  OUTPUT TRIM", _calSteps);
    _CalHeader(title);
    display.setTextSize(1);
    display.setCursor(0, 13);
    display.println("All outputs -> max.");
    display.println("Adjust each trimmer");
    display.println("so each jack reads");
    display.println("5.00V (multimeter).");
    display.println("");
    display.print("Click enc. to proceed");
    _CalFlush();
    _CalWaitClick();

    Serial.println("  Output trim done (MAXDAC trimmed to 5.00V).");
}

// ── Phase 2: Output low-point offset capture ─────────────────────────────────
static void _CalOutputOffset(CalibrationData &newCal) {
    DACWriteAll(CAL_DAC_LOW_CODE, CAL_DAC_LOW_CODE, CAL_DAC_LOW_CODE,
                CAL_DAC_LOW_CODE);
    if (_calOuts > NUM_OUTPUTS)
        DACWriteAllExp(CAL_DAC_LOW_CODE, CAL_DAC_LOW_CODE, CAL_DAC_LOW_CODE,
                       CAL_DAC_LOW_CODE);
    delay(50);

    for (int ch = 0; ch < _calOuts; ch++) {
        char title[24];
        snprintf(title, sizeof(title), "2/%d  %s OFFSET", _calSteps, CAL_OUT_NAMES[ch]);
        char prompt[24];
        snprintf(prompt, sizeof(prompt), "Measure %s, dial:", CAL_OUT_NAMES[ch]);
        int measuredMV = _CalEnterMV(title, prompt, CAL_DAC_LOW_MV);

        // Two (desired counts, command code) points:
        //   low : (measured→counts, CAL_DAC_LOW_CODE)   high: (MAXDAC, MAXDAC)
        // Invert the line to  cmd = dacScale*desired + dacOffset.
        float measuredCounts = (float)measuredMV * (float)MAXDAC / 5000.0f;
        float denom = (float)MAXDAC - measuredCounts;
        if (fabsf(denom) < 1.0f) {
            // Degenerate (measured ≈ 5V) — cannot fit; keep this channel identity.
            newCal.dacScale[ch] = 1.0f;
            newCal.dacOffset[ch] = 0.0f;
        } else {
            float scale = (float)(MAXDAC - CAL_DAC_LOW_CODE) / denom;
            float offset = (float)MAXDAC - scale * (float)MAXDAC;
            newCal.dacScale[ch] = scale;
            newCal.dacOffset[ch] = offset;
        }
        Serial.printf("  %s: measured=%dmV -> dacScale=%.4f dacOffset=%.2f\n",
                      CAL_OUT_NAMES[ch], measuredMV, newCal.dacScale[ch],
                      newCal.dacOffset[ch]);
    }

    DACWriteAll(0, 0, 0, 0);
    delay(50);
}

// ── CV capture step: wait for stable reference, then average ─────────────────
static uint16_t _CalCaptureCV(int ch, int refMV, int step) {
    char header[24];
    snprintf(header, sizeof(header), "%d/%d  CV%d INPUT %dV", step, _calSteps, ch + 1,
             refMV / 1000);

    while (true) {
        uint16_t liveRaw = _CalReadADCRaw(CV_IN_PINS[ch]);
        uint32_t liveMV = _CalRawToMVDisplay(liveRaw);

        _CalHeader(header);
        display.setTextSize(1);
        display.setCursor(0, 13);
        display.printf("Apply %dV to CV%d.\n\n", refMV / 1000, ch + 1);
        display.printf("Reading: %d.%03dV\n", (int)(liveMV / 1000),
                       (int)(liveMV % 1000));
        display.println("");
        display.print("Click when stable.");
        _CalFlush();

        // Poll button without blocking; _CalFlush already adds ~35 ms per frame
        if (digitalRead(ENCODER_SW) == LOW) {
            delay(20); // debounce
            if (digitalRead(ENCODER_SW) == LOW) {
                uint16_t averaged = _CalReadADC(CV_IN_PINS[ch]);
                uint32_t capturedMV = _CalRawToMVDisplay(averaged);
                Serial.printf("  CV%d ref=%dmV -> ADC=%d (~%dmV display)\n", ch + 1,
                              refMV, averaged, (int)capturedMV);
                while (digitalRead(ENCODER_SW) == LOW)
                    delay(10);
                delay(20);
                return averaged;
            }
        }
    }
}

// ── Main entry point ──────────────────────────────────────────────────────────
void RunCalibration() {
    Serial.println("Entering calibration mode...");

    // Probe the DAC bus before drawing anything: an expander adds four output
    // jacks to trim and one CV input to capture, which changes the step count
    // the wizard advertises.
    if (ProbeExpander()) {
        InitExpDAC(); // its channels need VREF/gain set before it will output
        _calOuts = NUM_MAX_OUTPUTS;
        _calCvIns = NUM_MAX_CV_INS;
    } else {
        _calOuts = NUM_OUTPUTS;
        _calCvIns = NUM_CV_INS;
    }
    _calSteps = 2 + 2 * _calCvIns;

    _CalHeader("CALIBRATION");
    display.setTextSize(1);
    display.setCursor(0, 13);
    display.printf("%d-step wizard:\n", _calSteps);
    display.println("1) Trim outputs to 5V");
    display.println("2) Measure outs @1V");
    display.printf("3-%d) Apply 1V & 3V to\n", _calSteps);
    display.println("     each CV input.");
    if (_calOuts > NUM_OUTPUTS)
        display.println("Expander detected.");
    display.print("Click enc. to start");
    _CalFlush();
    _CalWaitClick();

    CalibrationData newCal;
    newCal.magic = CAL_MAGIC;
    newCal.valid = true;

    // Seed every channel with the nominal mapping, including the ones this run
    // will not visit. The struct is sized to NUM_MAX_* whether or not an
    // expander is attached, so without this the unvisited entries would be
    // whatever was on the stack — and they get written to /cal.bin all the same,
    // to be read back as a channel's calibration the day one is fitted.
    for (int i = 0; i < NUM_MAX_OUTPUTS; i++) {
        newCal.dacScale[i] = 1.0f;
        newCal.dacOffset[i] = 0.0f;
    }
    for (int i = 0; i < NUM_MAX_CV_INS; i++) {
        newCal.cvScale[i] = 5000.0f / (float)MAXADC;
        newCal.cvOffset[i] = 0.0f;
    }

    // Output steps write RAW codes so the user trims/measures true hardware; the
    // stored correction must not fold back into the calibration measurements.
    SetDACCalBypass(true);

    _CalOutputTrim();
    _CalOutputOffset(newCal);

    SetDACCalBypass(false); // restore normal (corrected) DAC writes

    // ── Steps 3–6: per-channel CV input, per-reference capture ─────────────────
    const int refs[2] = {CAL_REF1_MV, CAL_REF2_MV};
    for (int ch = 0; ch < _calCvIns; ch++) {
        uint16_t rawRef[2];
        for (int r = 0; r < 2; r++) {
            int step = 3 + ch * 2 + r; // 3,4 then 5,6 then (expander) 7,8
            rawRef[r] = _CalCaptureCV(ch, refs[r], step);
        }
        // Linear fit through (rawRef[0], 1000mV) and (rawRef[1], 3000mV).
        // Identical readings would divide by zero — that means the two captures
        // saw the same voltage, so keep the nominal mapping for this channel
        // rather than storing an infinity that poisons every later reading.
        if (rawRef[1] == rawRef[0]) {
            newCal.cvScale[ch] = 5000.0f / (float)MAXADC;
            newCal.cvOffset[ch] = 0.0f;
            Serial.printf("  CV%d: identical captures — keeping nominal scale.\n", ch + 1);
            continue;
        }
        float scale = (float)(CAL_REF2_MV - CAL_REF1_MV) / (float)(rawRef[1] - rawRef[0]);
        float offset = CAL_REF1_MV - scale * rawRef[0];
        newCal.cvScale[ch] = scale;
        newCal.cvOffset[ch] = offset;
        Serial.printf("  CV%d: scale=%.4f  offset=%.2f\n", ch + 1, scale, offset);
    }

    // ── Summary — user confirms before saving ─────────────────────────────────
    _CalHeader("CALIBRATION DONE");
    display.setTextSize(1);
    display.setCursor(0, 13);
    display.println("Calibration done!");
    for (int ch = 0; ch < _calCvIns; ch++) {
        display.printf("CV%d: x%.4f+%.1f\n", ch + 1, newCal.cvScale[ch],
                       newCal.cvOffset[ch]);
    }
    display.println("");
    display.println("Click enc. to save");
    display.print("and reboot.");
    _CalFlush();

    _CalWaitClick();

    SaveCalibration(newCal);
    cal = newCal;
    Serial.println("Calibration saved. Rebooting...");

    _CalHeader("SAVED");
    display.setTextSize(2);
    display.setCursor(10, 25);
    display.println("Calibration");
    display.setCursor(30, 43);
    display.println("Saved!");
    _CalFlush();
    delay(1500);

    rp2040.reboot();
}
